hmatuschek/tinyi2c/firmware/temp.c

#include "temp.h"
#include <avr/interrupt.h>


#ifndef ISR
#define ISR(x) void x()
#endif

volatile uint16_t tempSum;
volatile uint16_t currentExtTemp;
volatile uint16_t currentIntTemp;
uint8_t sumCount;


void temp_init() {
  DDRB  &= ~(1<<DDB3);
  PORTB &= ~(1<<DDB3);
  DIDR0 |=  (1<<ADC3D);

  // Config ADC (Vcc ref, right adjust, selected pin)
  ADMUX   = (0<<REFS2) | (0<<REFS1) | (0<<REFS0) | (0<<ADLAR) | 0x03;
  // config prescaler to 128
  ADCSRA |= (1<<ADPS2) | (1<<ADPS1) | (1<<ADPS0);
  // enable ADC
  ADCSRA |= (1<<ADEN);

  // Config timer 0
  TCCR0A = 0;
  TCCR0B = (1<<CS02) | (0<<CS01) | (1<<CS00);
  TIMSK |= (1<<TOIE0);

  tempSum    = 0;
  currentExtTemp = 0;
  currentIntTemp = 0;
  sumCount   = 0;
}


int16_t
temp_get_ext() {
  return ((((int32_t)currentExtTemp)*98) >> 8) - 7302;
}

int16_t
temp_get_int() {
  return ((((int32_t)currentIntTemp)*1092) >> 8) - 67000;
}


//ISR(TIMER0_OVF_vect) {
void temp_poll() {
  // If still converting -> skip
  if (ADCSRA & (1<<ADSC))
    return;

  // if ready -> add value to sum
  tempSum += ADC;

  // increment sum counter
  sumCount++;
  if (64 == sumCount) {
    // Once complete ...
    // Store result and swap source
    if (0x03 == (ADMUX & 0x0f)) {
      currentExtTemp = tempSum;
      // select core temp
      ADMUX = (0<<REFS2) | (1<<REFS1) | (0<<REFS0) | (0<<ADLAR) | 0x0f;
    } else {
      currentIntTemp = tempSum;
      // select ext temp
      ADMUX = (0<<REFS2) | (0<<REFS1) | (0<<REFS0) | (0<<ADLAR) | 0x03;
    }
    tempSum = 0; sumCount = 0;
  }

  // restart conversion
  ADCSRA |= (1<<ADSC);
}

ISR(TIMER0_OVF_vect) {
  temp_poll();
}
